mcamposv/cw-pokemon-keyboard/debug/photo_2026-09-25_17-01-00.jpg

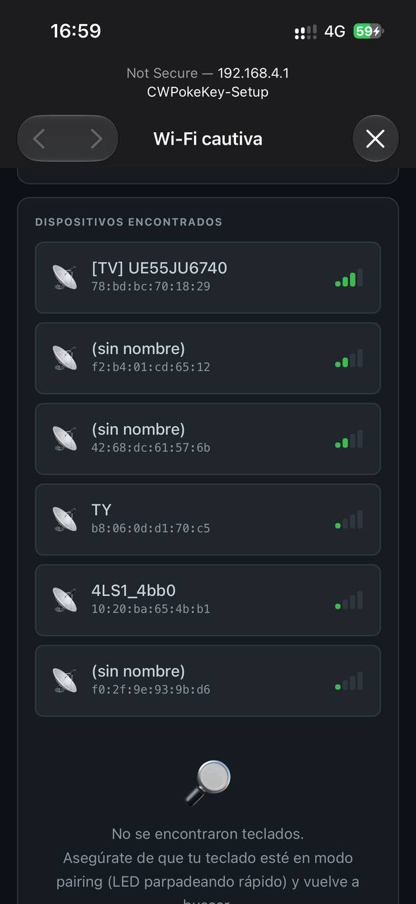
debug/photo_2026-09-25_17-01-00.jpg
