mcamposv/cw-pokemon-keyboard/firmware-s3/src/keymap.c

/* keymap.c — compiled as C11 so designated initializers are valid */
#include "keymap.h"

const uint16_t HID_TO_PS2[256] = {
    /* ── Letters ─────────────────────────────────────────────────────────── */
    [0x04] = 0x001C, /* A */
    [0x05] = 0x0032, /* B */
    [0x06] = 0x0021, /* C */
    [0x07] = 0x0023, /* D */
    [0x08] = 0x0024, /* E */
    [0x09] = 0x002B, /* F */
    [0x0A] = 0x0034, /* G */
    [0x0B] = 0x0033, /* H */
    [0x0C] = 0x0043, /* I */
    [0x0D] = 0x003B, /* J */
    [0x0E] = 0x0042, /* K */
    [0x0F] = 0x004B, /* L */
    [0x10] = 0x003A, /* M */
    [0x11] = 0x0031, /* N */
    [0x12] = 0x0044, /* O */
    [0x13] = 0x004D, /* P */
    [0x14] = 0x0015, /* Q */
    [0x15] = 0x002D, /* R */
    [0x16] = 0x001B, /* S */
    [0x17] = 0x002C, /* T */
    [0x18] = 0x003C, /* U */
    [0x19] = 0x002A, /* V */
    [0x1A] = 0x001D, /* W */
    [0x1B] = 0x0022, /* X */
    [0x1C] = 0x0035, /* Y */
    [0x1D] = 0x001A, /* Z */

    /* ── Numbers ──────────────────────────────────────────────────────────── */
    [0x1E] = 0x0016, /* 1 */
    [0x1F] = 0x001E, /* 2 */
    [0x20] = 0x0026, /* 3 */
    [0x21] = 0x0025, /* 4 */
    [0x22] = 0x002E, /* 5 */
    [0x23] = 0x0036, /* 6 */
    [0x24] = 0x003D, /* 7 */
    [0x25] = 0x003E, /* 8 */
    [0x26] = 0x0046, /* 9 */
    [0x27] = 0x0045, /* 0 */

    /* ── Control & punctuation ────────────────────────────────────────────── */
    [0x28] = 0x005A, /* Enter      */
    [0x29] = 0x0076, /* Escape     */
    [0x2A] = 0x0066, /* Backspace  */
    [0x2B] = 0x000D, /* Tab        */
    [0x2C] = 0x0029, /* Space      */
    [0x2D] = 0x004E, /* -/_  (US) | '/? (ES) */
    [0x2E] = 0x0055, /* =/+  (US) | ¡  (ES)  */
    [0x2F] = 0x0054, /* [/{  (US) | `/^ (ES) */
    [0x30] = 0x005B, /* ]/}  (US) | +/* (ES) */
    [0x31] = 0x005D, /* \/|                  */
    [0x32] = 0x005D, /* Non-US #/~ (ISO)     */
    [0x33] = 0x004C, /* ;/:  (US) | ñ/Ñ (ES) */
    [0x34] = 0x0052, /* '/"  (US) | ´/¨ (ES) */
    [0x35] = 0x000E, /* `/~  (US) | º/ª (ES) */
    [0x36] = 0x0041, /* ,/<  */
    [0x37] = 0x0049, /* ./>  */
    [0x38] = 0x004A, /* //?  */

    /* ── Lock keys ────────────────────────────────────────────────────────── */
    [0x39] = 0x0058, /* Caps Lock   */
    [0x47] = 0x007E, /* Scroll Lock */
    [0x53] = 0x0077, /* Num Lock    */

    /* ── Function keys ────────────────────────────────────────────────────── */
    [0x3A] = 0x0005, /* F1  */
    [0x3B] = 0x0006, /* F2  */
    [0x3C] = 0x0004, /* F3  */
    [0x3D] = 0x000C, /* F4  */
    [0x3E] = 0x0003, /* F5  */
    [0x3F] = 0x000B, /* F6  */
    [0x40] = 0x0083, /* F7  */
    [0x41] = 0x000A, /* F8  */
    [0x42] = 0x0001, /* F9  */
    [0x43] = 0x0009, /* F10 */
    [0x44] = 0x0078, /* F11 */
    [0x45] = 0x0007, /* F12 */

    /* ── Navigation cluster (extended) ────────────────────────────────────── */
    [0x49] = 0x0170, /* Insert    (E0 70) */
    [0x4A] = 0x016C, /* Home      (E0 6C) */
    [0x4B] = 0x017D, /* Page Up   (E0 7D) */
    [0x4C] = 0x0171, /* Delete    (E0 71) */
    [0x4D] = 0x0169, /* End       (E0 69) */
    [0x4E] = 0x017A, /* Page Down (E0 7A) */

    /* ── Arrow keys (extended) ────────────────────────────────────────────── */
    [0x4F] = 0x0174, /* Right (E0 74) */
    [0x50] = 0x016B, /* Left  (E0 6B) */
    [0x51] = 0x0172, /* Down  (E0 72) */
    [0x52] = 0x0175, /* Up    (E0 75) */

    /* ── Numpad ───────────────────────────────────────────────────────────── */
    [0x54] = 0x014A, /* Kp /     (E0 4A) */
    [0x55] = 0x007C, /* Kp *              */
    [0x56] = 0x007B, /* Kp -              */
    [0x57] = 0x0079, /* Kp +              */
    [0x58] = 0x015A, /* Kp Enter (E0 5A)  */
    [0x59] = 0x0069, /* Kp 1 / End        */
    [0x5A] = 0x0072, /* Kp 2 / Down       */
    [0x5B] = 0x007A, /* Kp 3 / PgDn       */
    [0x5C] = 0x006B, /* Kp 4 / Left       */
    [0x5D] = 0x0073, /* Kp 5              */
    [0x5E] = 0x0074, /* Kp 6 / Right      */
    [0x5F] = 0x006C, /* Kp 7 / Home       */
    [0x60] = 0x0075, /* Kp 8 / Up         */
    [0x61] = 0x007D, /* Kp 9 / PgUp       */
    [0x62] = 0x0070, /* Kp 0 / Ins        */
    [0x63] = 0x0071, /* Kp . / Del        */

    /* ── ISO extra key (between LShift and Z on ES/EU keyboards) ──────────── */
    [0x64] = 0x0061, /* < / > / | */

    /* ── Application / Menu key ──────────────────────────────────────────── */
    [0x65] = 0x012F, /* Menu (E0 2F) */

    /* ── Modifiers (also decoded from report byte 0) ─────────────────────── */
    [0xE0] = 0x0014, /* Left  Ctrl              */
    [0xE1] = 0x0012, /* Left  Shift             */
    [0xE2] = 0x0011, /* Left  Alt               */
    [0xE3] = 0x011F, /* Left  GUI  (E0 1F)      */
    [0xE4] = 0x0114, /* Right Ctrl (E0 14)      */
    [0xE5] = 0x0059, /* Right Shift             */
    [0xE6] = 0x0111, /* Right Alt / AltGr (E0 11) */
    [0xE7] = 0x0127, /* Right GUI  (E0 27)      */
};

const uint16_t MODIFIER_TO_PS2[8] = {
    0x0014, /* bit 0: Left  Ctrl              */
    0x0012, /* bit 1: Left  Shift             */
    0x0011, /* bit 2: Left  Alt               */
    0x011F, /* bit 3: Left  GUI  (E0 1F)      */
    0x0114, /* bit 4: Right Ctrl (E0 14)      */
    0x0059, /* bit 5: Right Shift             */
    0x0111, /* bit 6: Right Alt / AltGr       */
    0x0127, /* bit 7: Right GUI  (E0 27)      */
};
